abusetech/DoorSensor/src/adxl345.h

#pragma once
#include "common.h"
#include "softi2c.h"
#include <avr/io.h>
#include <stdint.h>

#define ADXL_I2C_ADDR       (0x1D)
#define ADXL_BW_RATE        (0x2C)
#define ADXL_POWER_CTL      (0x2D)
#define ADXL_DATA_FORMAT    (0x31)
#define ADXL_DATAX0         (0x32)
#define ADXL_FIFO_CTL       (0x38)

//FIFO_CTL bits

#define ADXL_FIFO_MODE_BYPASS  0
#define ADXL_FIFO_MODE_FIFO    1
#define ADXL_FIFO_MODE_STREAM  2
#define ADXL_FIFO_MODE_TIRGGER 3

//POWER_CTL bits

#define ADXL_POWER_LINK         (1 << 5)
#define ADXL_POWER_AUTO_SLEEP   (1 << 4)
#define ADXL_POWER_MEASURE      (1 << 3)
#define ADXL_POWER_SLEEP        (1 << 2)

typedef struct {
    int16_t datax;
    int16_t datay;
    int16_t dataz;
} adxl_data_t;

class ADXL345{
    private:
        SoftI2C& i2c;
    public:
        ADXL345(SoftI2C& i2c);
        adxl_data_t readFifo();
        void fifoCtl(uint8_t fifoMode, uint8_t trigger, uint8_t samples);
        void powerCtl(uint8_t flags, uint8_t wakeup);
        void bwRate(uint8_t low_power, uint8_t rate);
};
