abusetech/DoorSensor/src/spi.hpp

#pragma once
#include <avr/io.h>

class SPI {  
    private:
        uint8_t ss_pin;
        volatile uint8_t * ss_port;
    public:
        SPI(volatile uint8_t * ss_port, uint8_t ss_pin);
        void begin();
        void end();
        uint8_t SPI::transfer(uint8_t b);
        uint8_t SPI::transferByte(uint8_t b);
        void transfer(uint8_t * buffer, uint8_t size);
        void write(const uint8_t * buffer, uint8_t size);
};
